kanengomibako/Sodium/KiCad/Sodium.sch

## KiCad design KiCad/Sodium.sch (2021-05-10)

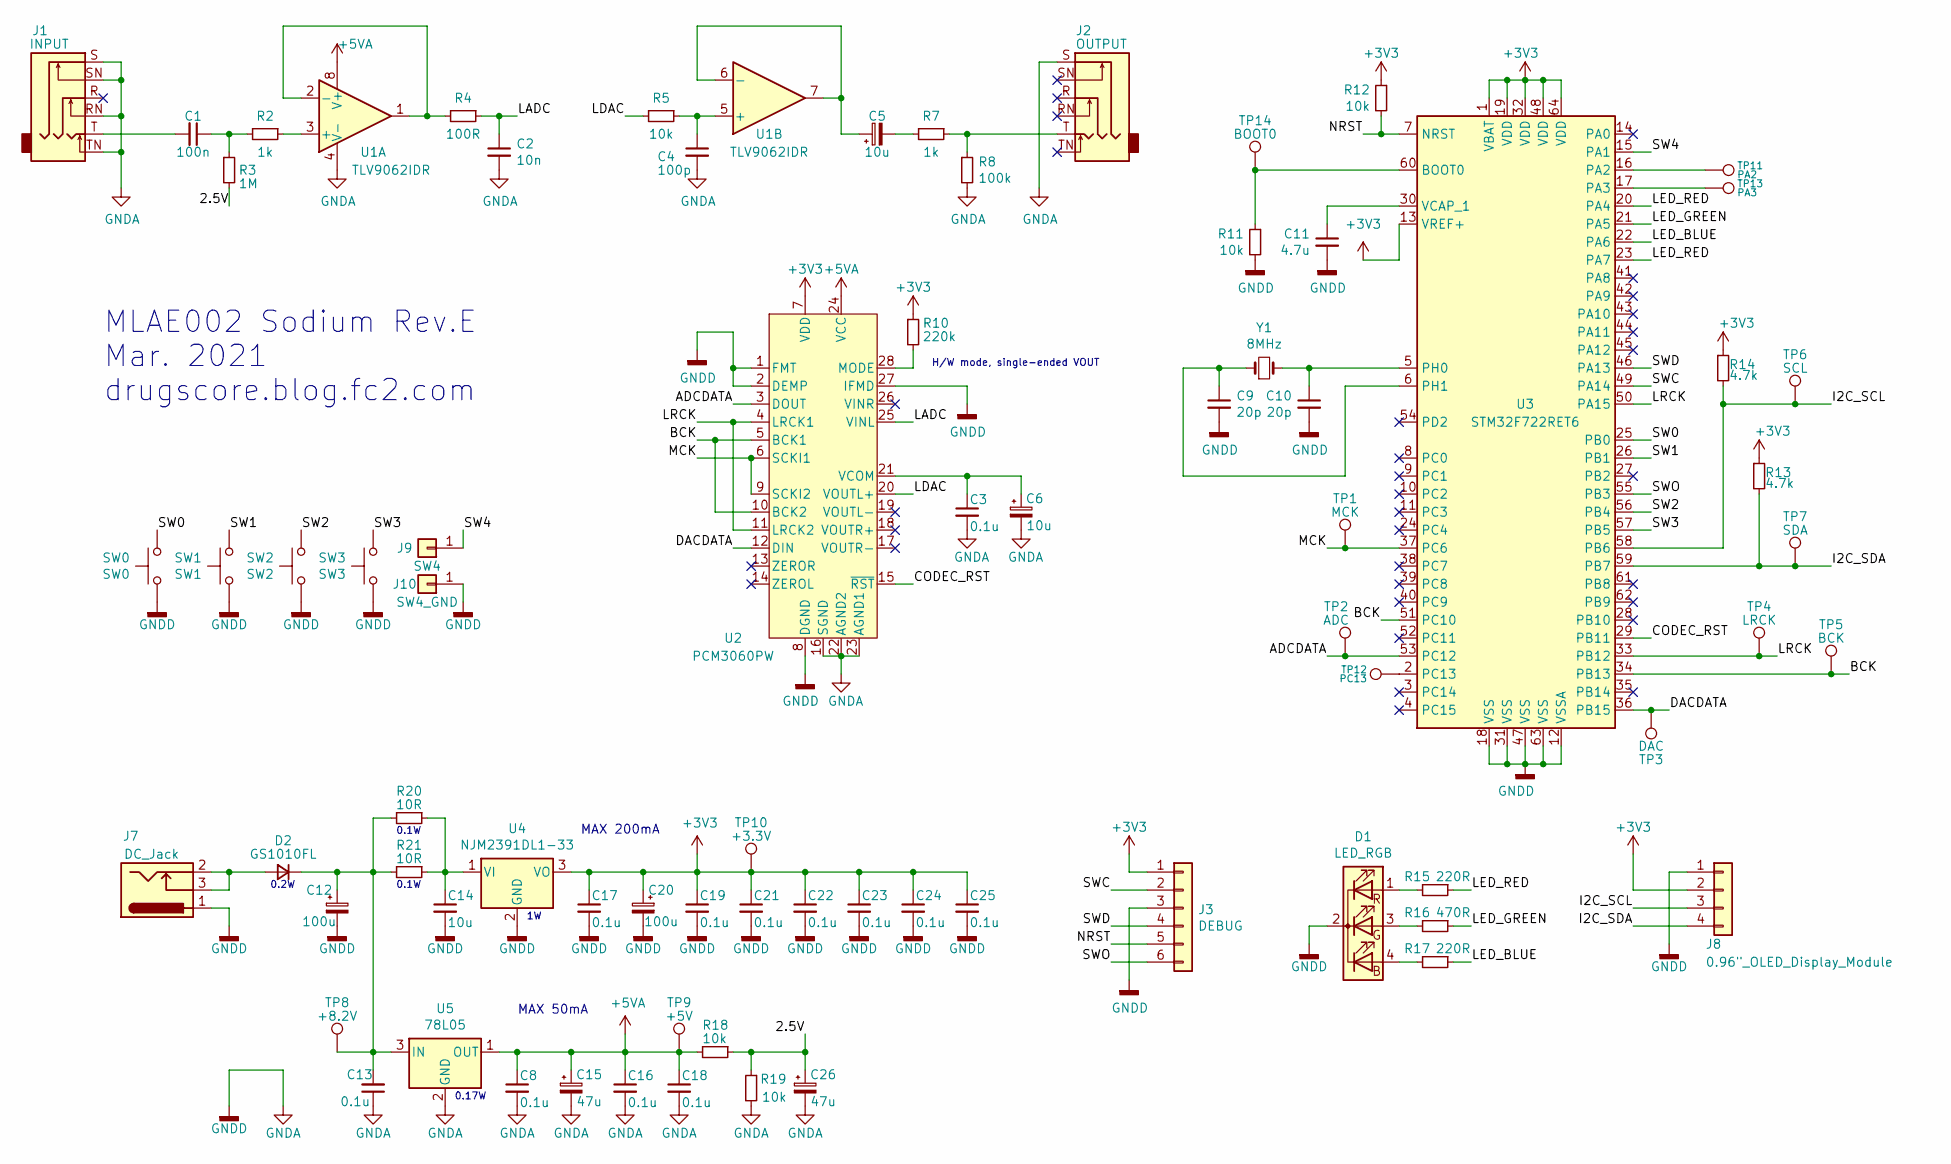
[picture p21: schematic Sodium.sch]

Parts:
C1: 100n; C_0805_2012Metric
C2: 10n; C_0603_1608Metric
C3, C8, C13, C16, C17, C18, C19, C21, C22, C23, C24, C25: 0.1u; C_0603_1608Metric
C4: 100p; C_0603_1608Metric
C5, C6: 10u; CP_Elec_4x3
C9, C10: 20p; C_0603_1608Metric
C11: 4.7u; C_0805_2012Metric
C12, C20: 100u; CP_Elec_6.3x5.4
C14: 10u; C_0805_2012Metric
C15, C26: 47u; CP_Elec_4x3
D1: LED_RGB; my_LED_5mm_RGB_mirror
D2: GS1010FL; D_SOD-123F
J1: INPUT; my_Phone_Jack_Daier
J2: OUTPUT; my_Phone_Jack_Daier
J3: DEBUG; PinHeader_1x06_P2.54mm_Horizontal
J7: DC_Jack; my_DC_Jack
J8: 0.96\"_OLED_Display_Module; OLED_Display_0.96inch
J9: SW4; PinHeader_1x01_P2.54mm_Vertical
J10: SW4_GND; PinHeader_1x01_P2.54mm_Vertical
R2, R7: 1k; R_0805_2012Metric
R3: 1M; R_0603_1608Metric
R4: 100R; R_0805_2012Metric
R5, R11, R12, R18, R19: 10k; R_0603_1608Metric
R8: 100k; R_0603_1608Metric
R10: 220k; R_0603_1608Metric
R13, R14: 4.7k; R_0603_1608Metric
R15, R17: 220R; R_0805_2012Metric
R16: 470R; R_0805_2012Metric
R20, R21: 10R; R_1210_3225Metric
SW0: SW0; my_SW_PUSH_12mm
SW1: SW1; my_SW_PUSH_12mm
SW2: SW2; my_SW_PUSH_12mm
SW3: SW3; my_SW_PUSH_12mm
TP1: MCK; my_TestPoint_1.2mm
TP2: ADC; my_TestPoint_1.2mm
TP3: DAC; my_TestPoint_1.2mm
TP4: LRCK; my_TestPoint_1.2mm
TP5: BCK; my_TestPoint_1.2mm
TP6: SCL; my_TestPoint_1.2mm
TP7: SDA; my_TestPoint_1.2mm
TP8: +8.2V; my_TestPoint_1.2mm
TP9: +5V; my_TestPoint_1.2mm
TP10: +3.3V; my_TestPoint_1.2mm
TP11: PA2; my_TestPoint_1.2mm
TP12: PC13; my_TestPoint_1.2mm
TP13: PA3; my_TestPoint_1.2mm
TP14: BOOT0; my_TestPoint_1.2mm
U1: TLV9062IDR; my_SOIC-8_3.9x4.9mm_Pitch1.27mm
U2: PCM3060PW; CS4272(TSSOP28)
U3: STM32F722RET6; my_LQFP-64_10x10_P0.5_narrow
U4: NJM2391DL1-33; my_DPAK_TO-252-2
U5: 78L05; SOT-89-3
Y1: 8MHz; Crystal_SMD_HC49-SD

Connections:
2.5V: C26.1, R3.2, R18.1, R19.1
+3V3: C17.1, C19.1, C20.1, C21.1, C22.1, C23.1, C24.1, C25.1, J3.1, J8.2, R10.1, R12.1, R13.1, R14.1, TP10.1, U2.7 (VDD), U3.1 (VBAT), U3.13 (VREF+), U3.19 (VDD), U3.32 (VDD), U3.48 (VDD), U3.64 (VDD), U4.3 (VO)
+5VA: C8.1, C15.1, C16.1, C18.1, R18.2, TP9.1, U1.8 (V+), U2.24 (VCC), U5.1 (OUT)
ADCDATA: TP2.1, U2.3 (DOUT), U3.53 (PC12)
BCK: TP5.1, U2.5 (BCK1), U2.10 (BCK2), U3.34 (PB13), U3.51 (PC10)
CODEC_RST: U2.15 (~RST), U3.29 (PB11)
DACDATA: TP3.1, U2.12 (DIN), U3.36 (PB15)
GNDA: C2.2, C3.2, C4.2, C6.2, C8.2, C9.2, C10.2, C11.2, C12.2, C13.1, C14.2, C15.2, C16.2, C17.2, C18.2, C19.2, C20.2, C21.2, C22.2, C23.2, C24.2, C25.2, C26.2, D1.2 (K), J1.RN, J1.S, J1.SN, J1.TN, J2.S, J3.3, J7.1, J8.1, J10.1, R8.2, R11.2, R19.2, SW0.2, SW1.2, SW2.2, SW3.2, U1.4 (V-), U2.1 (FMT), U2.2 (DEMP), U2.8 (DGND), U2.16 (SGND), U2.22 (AGND2), U2.23 (AGND1), U2.27 (IFMD), U3.12 (VSSA), U3.18 (VSS), U3.31 (VSS), U3.47 (VSS), U3.63 (VSS), U4.2 (GND), U5.2 (GND)
I2C_SCL: J8.3, R14.2, TP6.1, U3.58 (PB6)
I2C_SDA: J8.4, R13.2, TP7.1, U3.59 (PB7)
LADC: C2.1, R4.1, U2.25 (VINL)
LDAC: R5.2, U2.20 (VOUTL+)
LED_BLUE: R17.1, U3.22 (PA6)
LED_GREEN: R16.1, U3.21 (PA5)
LED_RED: R15.1, U3.20 (PA4), U3.23 (PA7)
LRCK: TP4.1, U2.4 (LRCK1), U2.11 (LRCK2), U3.33 (PB12), U3.50 (PA15)
MCK: TP1.1, U2.6 (SCKI1), U2.9 (SCKI2), U3.37 (PC6)
NRST: J3.5, R12.2, U3.7 (NRST)
unnamed: C1.1, R2.2, R3.1
unnamed: C1.2, J1.T
unnamed: C3.1, C6.1, U2.21 (VCOM)
unnamed: C4.1, R5.1, U1.5 (+)
unnamed: C5.1, U1.6 (-), U1.7
unnamed: C5.2, R7.2
unnamed: C9.1, U3.6 (PH1), Y1.1
unnamed: C10.1, U3.5 (PH0), Y1.2
unnamed: C11.1, U3.30 (VCAP_1)
unnamed: C12.1, C13.2, D2.1 (K), R20.2, R21.2, TP8.1, U5.3 (IN)
unnamed: C14.1, R20.1, R21.1, U4.1 (VI)
unnamed: D1.1 (RA), R15.2
unnamed: D1.3 (GA), R16.2
unnamed: D1.4 (BA), R17.2
unnamed: D2.2 (A), J7.2, J7.3
unnamed: J2.T, R7.1, R8.1
unnamed: R2.1, U1.3 (+)
unnamed: R4.2, U1.1, U1.2 (-)
unnamed: R10.2, U2.28 (MODE)
unnamed: R11.1, TP14.1, U3.60 (BOOT0)
unnamed: TP11.1, U3.16 (PA2)
unnamed: TP12.1, U3.2 (PC13)
unnamed: TP13.1, U3.17 (PA3)
SW0: SW0.1, U3.25 (PB0)
SW1: SW1.1, U3.26 (PB1)
SW2: SW2.1, U3.56 (PB4)
SW3: SW3.1, U3.57 (PB5)
SW4: J9.1, U3.15 (PA1)
SWC: J3.2, U3.49 (PA14)
SWD: J3.4, U3.46 (PA13)
SWO: J3.6, U3.55 (PB3)

Notes on the sheet:
H/W mode, single-ended VOUT
MLAE002 Sodium Rev.E Mar. 2021 drugscore.blog.fc2.com
MAX 50mA
MAX 200mA
0.2W
0.17W
0.1W
