kanengomibako/Sodium/Src/example/main.cpp

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
/* Includes ------------------------------------------------------------------*/
#include "main.h"


I2C_HandleTypeDef hi2c1;

I2S_HandleTypeDef hi2s2;
I2S_HandleTypeDef hi2s3;
DMA_HandleTypeDef hdma_spi2_tx;
DMA_HandleTypeDef hdma_spi3_rx;

void SystemClock_Config(void);
static void MX_GPIO_Init(void);
static void MX_DMA_Init(void);
static void MX_I2C1_Init(void);
static void MX_I2S2_Init(void);
static void MX_I2S3_Init(void);
/* USER CODE BEGIN 0 */
#include "user_main.hpp"

/* USER CODE END 0 */

/**
  * @brief  The application entry point.
  * @retval int
  */
int main(void)
{
  /* Enable D-Cache---------------------------------------------------------*/
  SCB_EnableDCache();

  /* MCU Configuration--------------------------------------------------------*/

  /* Reset of all peripherals, Initializes the Flash interface and the Systick. */
  HAL_Init();

  /* Configure the system clock */
  SystemClock_Config();

  /* Initialize all configured peripherals */
  MX_GPIO_Init();
  MX_DMA_Init();
  MX_I2C1_Init();
  MX_I2S2_Init();
  MX_I2S3_Init();
  /* USER CODE BEGIN 2 */
  mainInit();
  /* USER CODE END 2 */

  /* Infinite loop */
  /* USER CODE BEGIN WHILE */
  while (1)
  {
    /* USER CODE END WHILE */

    /* USER CODE BEGIN 3 */
    mainLoop();
  }
  /* USER CODE END 3 */
}

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
